baseunder/AnalogWallet/py/pw_check.py

import re

def password_check(password):
    """
    Verify the strength of 'password'
    Returns a dict indicating the wrong criteria
    A password is considered strong if:
        8 characters length or more
        1 digit or more
        1 symbol or more
        1 uppercase letter or more
        1 lowercase letter or more
    """
    # calculating the length
    length_error = len(password) < 8
    # searching for digits
    digit_error = re.search(r"\d", password) is None
    # searching for uppercase
    uppercase_error = re.search(r"[A-Z]", password) is None
    # searching for lowercase
    lowercase_error = re.search(r"[a-z]", password) is None
    # searching for symbols
    symbol_error = re.search(r"[ ?!#$%&'()*+,-./[\\\]^_`{|}~"+r'"]', password) is None
    # overall result
    password_ok = not ( length_error or digit_error or uppercase_error or lowercase_error or symbol_error )
    if not password_ok:
        print("""password needs to have:
        8 characters length or more
        1 digit or more
        1 symbol or more
        1 uppercase letter or more
        1 lowercase letter or more""")
    return password_ok
